mechanical-software-inc/MS1_board/Kristerj.kicad_sch

## KiCad design Kristerj.kicad_sch (2024-08-09)

Schematic: Kristerj.kicad_sch

Parts:
C1, C2, C3, C4: 47uF; C_1206_3216Metric; Mfg PN C3216X5R1E476M160AC
C5: 22uF; C_0603_1608Metric; Mfg PN GRM188R61A226ME15D
C6, C7, C18, C19, C31, C32, C37, C41, C42, C43, C44, C45, C46, C47, C48, C49, C50, C51, C52, C53, C54, C55, C56, C57, C58, C59, C60, C64, C66, C68: 100nF; C_0603_1608Metric; Mfg PN C1608X7R1H104K080AA
C8, C9, C20, C21, C33, C61: 1uF; C_0603_1608Metric; Mfg PN CL10A105KL8NNNC
C10, C13, C16, C17, C24, C25, C28, C29, C36, C40: 0.01uF; C_0603_1608Metric; Mfg PN C0603C103K5RAC7867
C11, C12, C14, C15, C22, C23, C26, C27, C35, C39: 220pF; C_0603_1608Metric; Mfg PN 06035A221JAT2A
C30: .022uF; C_0603_1608Metric; Mfg PN CGA3E2X7R1H223K080AA
C34, C38, C63, C65, C67, C69: T491A106K010AT; C_1206_3216Metric; Mfg PN T491A106K010AT
C62: 470pF; C_0603_1608Metric; Mfg PN GCM1885C2A471JA16D
D1, D2, D3, D4, D5, D6, D7, D8, D9, D10, D11, D12, D13, D14, D23, D24, D25, D26, D27, D28, D29, D30, D31, D32, D33, D34, D35, D36, D45, D47, D49, D50, D51, D53, D54, D55, D56, D57: 3.9V; D_SOD-323; Mfg PN MM3Z3V9ST1G
D15, D16, D21, D22, D37, D38, D43, D44, D59, D65: 5A; D_SMC; Mfg PN VS-5ECH06-M3/9AT
D17, D18, D19, D20, D39, D40, D41, D42, D63, D64: D; D_DO-41_SOD81_P7.62mm_Horizontal; Mfg PN 1N4007-T
F1: 3A; Fuse_Bourns_MF-RHT200; Mfg PN MF-RHT200/32-2
FB1: 28C0236-0JW-10; LairdTech_28C0236-0JW-10; Mfg PN 28C0236-0JW-10
H1, H3, H4, H5, H8, H11: MountingHole; MountingHole_5.5mm; Mfg PN DNP
H2, H6, H7, H9, H10, H12, H13: MountingHole; MountingHole_3.5mm; Mfg PN DNP
IC1, IC2, IC3, IC4, IC5, IC6: LM4040C30FTA; SOT-23; Mfg PN LM4040C30FTA
J1: 24V IN; 1945096; Mfg PN 1945096
J2: +24V IN; BarrelJack_CUI_PJ-102AH_Horizontal; Mfg PN PJ-102AH
J3_1, J3_2, J4_1, J4_2, J9_1, J9_2, J10_1, J10_2, J11_1, J11_2, J12_1, J12_2, J15_1, J15_2, J16_1, J16_2, J17_1, J17_2, J18_1, J18_2, J21_1, J21_2: Screw_Terminal_01x04; PhoenixContact_MSTBA_2,5_4-G-5,08_1x04_P5.08mm_Horizontal; Mfg PN 1757268
J4: 5-2301994-9; TE_5-2301994-9; PARTREV A1
J5, J6, J13, J14, J19, J20: Conn_01x03; PinSocket_1x03_P2.54mm_Vertical; Mfg PN 215299-3
J7: Conn_01x02; 1945096; Mfg PN 1945096
J8: Conn_02x20_Odd_Even; PinHeader_2x20_P2.54mm_Vertical; Mfg PN 6-103169-8
JP1, JP2, JP3, JP4, JP5, JP6, JP7, JP8, JP9, JP10, JP11, JP12: SolderJumper_3_Open; SolderJumper-3_P1.3mm_Open_RoundedPad1.0x1.5mm
L1: 22uH; L_Radial_D7.0mm_P3.00mm; Mfg PN RLB0712-220KL
PS1: K7805-3AR3; CONV_K7805-3AR3; Mfg PN K7805-3AR3
Q1, Q2, Q7, Q8, Q13, Q14, Q19, Q20, Q25, Q31: DMN10H220L; SOT-23; Mfg PN DMN10H220L-7
Q3, Q4, Q9, Q10, Q15, Q16, Q21, Q22, Q27, Q33: RD3P130S; TO-252-2; Mfg PN RD3P130SPFRATL
Q5, Q6, Q17, Q18, Q30: NDC7002N; SOT-23-6; Mfg PN NDC7002N
Q11, Q12, Q23, Q24, Q36: IRF9Z24S; TO-263-2; Mfg PN IRF9Z24SPBF
Q37, Q38, Q39, Q40, Q41, Q42, Q43, Q44, Q45, Q46: MMBT3904; SOT-23; Mfg PN MMBT3904
R1, R3, R7, R9, R14, R16, R29, R31, R77, R79, R81, R83, R89, R92, R103, R105, R149, R153, R160, R175: 68K; R_0603_1608Metric; Mfg PN RC0603FR-0768KL
R2, R4, R8, R10, R11, R15, R17, R18, R19, R20, R22, R25, R30, R32, R33, R34, R35, R36, R47, R48, R55, R57, R69, R72, R78, R80, R82, R84, R85, R88, R90, R91, R93, R94, R95, R98, R104, R106, R107, R108, R109, R110, R121, R122, R127, R129, R143, R144, R150, R154, R157, R158, R161, R165, R166, R167, R169, R176, R179, R180, R181, R182, R193, R201, R215, R221, R222, R223, R224, R225, R226, R227, R228, R229, R230, R231, R232, R233, R234, R235, R236, R237, R238, R239, R240, R241, R242, R243, R244, R245, R246, R247, R248, R249, R250: 10K; R_0603_1608Metric; Mfg PN ERJ-3GEYJ103V
R5, R6, R49, R54: 5.1K; R_0603_1608Metric; Mfg PN ERJ-3EKF5101V
R12, R13, R21, R23, R27, R28, R42, R44, R64, R67, R86, R87, R96, R97, R101, R102, R116, R119, R136, R139, R159, R162, R168, R170, R173, R174, R188, R208: 150; R_0603_1608Metric; Mfg PN CR0603-JW-151ELF
R24, R26, R37, R38, R60, R62, R99, R100, R111, R113, R133, R134, R171, R172, R183, R205: 1K; R_0603_1608Metric; Mfg PN CR0603-FX-1001ELF
R39, R40, R112, R114, R185: 16K; R_0603_1608Metric; Mfg PN RK73H1JTTD1800F
R41, R43, R63, R66, R115, R118, R135, R138, R187, R207: 3.3K; R_0603_1608Metric; Mfg PN RC0603JR-103K3L
R45, R46, R65, R68, R117, R120, R137, R142, R189, R211: 100K; R_0603_1608Metric; Mfg PN RC0603JR-07100KL
R50, R51, R52, R53, R70, R71, R73, R76, R123, R124, R125, R126, R140, R141, R147, R148, R195, R198, R213, R219: 100; R_0603_1608Metric; Mfg PN RC0603FR-07100RL
R56, R58, R128, R130, R202: 6.2K; R_0603_1608Metric; Mfg PN CRCW06036K20FKEAC
R59, R61, R131, R132, R204: 249; R_0603_1608Metric; Mfg PN RK73H1JTTD2490F
R74, R75, R145, R146, R218: 22.1; R_0603_1608Metric; Mfg PN RK73H1JTTD22R1F
R251, R252, R253, R254: 10; R_0603_1608Metric; Mfg PN RMCF0603FT10R0
R255: 1.5k; R_0603_1608Metric; Mfg PN RC0603JR-071K5L
R256, R257, R258: 33; R_0603_1608Metric; Mfg PN RC0603FR-0733R2L
R259, R260: 332; R_0603_1608Metric; Mfg PN RMCF0603FT332R
R261: 12.1k; R_0603_1608Metric; Mfg PN RMCF0603FT12K1
U1, U2, U9, U10, U17, U18: PICO_RP2040; Rasp_Pi_PICO; Mfg PN M20-7822046
U3, U4, U7, U25, U26, U27: MCP3428x-xST; TSSOP-14_4.4x5mm_P0.65mm; Mfg PN MCP3428-E/ST
U5, U6, U13, U14, U22: Opamp_Dual_Generic; DFN-8-1EP_3x3mm_P0.5mm_EP1.65x2.38mm; Mfg PN LT1490ACDD#TRPBF
U8: LAN8720A; VQFN-24-1EP_4x4mm_P0.5mm_EP2.5x2.5mm_ThermalVias; Mfg PN LAN8720AI-CP-TR
U11: 24AA256UIDT-I/SN; SOIC-8_3.9x4.9mm_P1.27mm; Mfg PN 24AA256UIDT-I/SN
X1: ECS-2033-500-BN; Oscillator_SMD_ECS_2520MV-xxx-xx-4Pin_2.5x2.0mm; Mfg PN ECS-2033-500-BN

Connections:
3.3V_1: JP1.3 (B), JP7.3 (B), R35.2, R227.2, U2.36 (3V3)
3.3V_2: JP2.3 (B), JP8.3 (B), R107.2, R228.2, U9.36 (3V3)
3.3V_3: JP3.3 (B), JP9.3 (B), R179.2, R229.2, U17.36 (3V3)
3.3V_4: JP4.3 (B), JP10.3 (B), R33.2, R230.2, U1.36 (3V3)
3.3V_5: JP5.3 (B), JP11.3 (B), R109.2, R231.2, U10.36 (3V3)
3.3V_6: C60.1, FB1.2, JP6.3 (B), JP12.3 (B), R181.2, R232.2, R253.2, R255.2, U8.9 (VDDIO), U18.36 (3V3), X1.4 (VDD)
+5V: C5.2, C32.1, C34.1, C37.1, C38.1, C41.1, C63.1, C64.1, C65.1, C66.1, C67.1, C68.1, C69.1, J8.2, J8.4, PS1.9 (+VO1), PS1.10 (+VO1), R5.2, R6.2, R20.2, R24.1, R25.2, R26.1, R41.2, R43.2, R49.2, R54.2, R63.2, R66.2, R94.2, R95.2, R98.2, R99.1, R100.1, R115.2, R118.2, R135.2, R138.2, R165.2, R166.2, R167.2, R169.2, R171.1, R172.1, R187.2, R207.2, U1.40 (VBUS), U2.40 (VBUS), U3.6 (V_{DD}), U3.9 (Adr0), U4.6 (V_{DD}), U4.9 (Adr0), U7.6 (V_{DD}), U7.9 (Adr0), U7.10 (Adr1), U9.40 (VBUS), U10.40 (VBUS), U11.8 (VCC), U17.40 (VBUS), U18.40 (VBUS), U25.6 (V_{DD}), U26.6 (V_{DD}), U26.10 (Adr1), U27.6 (V_{DD})
+24V: C8.1, C9.1, C10.2, C13.2, C16.2, C17.2, C20.1, C21.1, C24.2, C25.2, C28.2, C29.2, C33.1, C36.2, C40.2, D17.1 (K), D19.1 (K), D39.1 (K), D41.1 (K), D63.1 (K), F1.1, J1.1, J2.1, J3_1.2, J3_1.4, J3_2.1, J3_2.4, J4_1.2, J4_1.4, J4_2.1, J4_2.4, J11_1.2, J11_1.4, J11_2.1, J11_2.4, J12_1.2, J12_1.4, J12_2.1, J12_2.4, J17_1.2, J17_1.4, J17_2.1, J17_2.4, J18_1.2, J18_1.4, J18_2.1, J18_2.4, Q3.3 (S), Q4.3 (S), Q9.3 (S), Q10.3 (S), Q15.3 (S), Q16.3 (S), Q21.3 (S), Q22.3 (S), Q27.3 (S), Q33.3 (S), R47.2, R48.2, R55.2, R57.2, R59.2, R61.2, R69.2, R72.2, R121.2, R122.2, R127.2, R129.2, R131.2, R132.2, R143.2, R144.2, R193.2, R201.2, R204.2, R215.2, U5.8 (V+), U6.8 (V+), U13.8 (V+), U14.8 (V+), U22.8 (V+)
ADC_REF1: IC2.1 (CATHODE), R26.2, U2.35 (ADC_VREF)
ADC_REF2: IC3.1 (CATHODE), R99.2, U9.35 (ADC_VREF)
ADC_REF3: IC5.1 (CATHODE), R171.2, U17.35 (ADC_VREF)
ADC_REF4: IC1.1 (CATHODE), R24.2, U1.35 (ADC_VREF)
ADC_REF5: IC4.1 (CATHODE), R100.2, U10.35 (ADC_VREF)
ADC_REF6: IC6.1 (CATHODE), R172.2, U18.35 (ADC_VREF)
AVDD: C30.2, FB1.1, J4.P9, J4.P12, U8.1 (VDD2A), U8.19 (VDD1A)
CRS: R254.2, U18.11 (GP8)
GND: C1.1, C2.1, C3.1, C4.1, C5.1, C6.2, C7.2, C8.2, C9.2, C18.2, C19.2, C20.2, C21.2, C30.1, C31.2, C32.2, C33.2, C34.2, C37.2, C38.2, C41.2, C42.2, C43.2, C44.2, C45.2, C46.2, C47.2, C48.2, C49.2, C50.2, C51.2, C52.2, C53.2, C54.2, C55.2, C56.2, C57.2, C58.2, C59.2, C60.2, C61.2, C62.1, C63.2, C64.2, C65.2, C66.2, C67.2, C68.2, C69.2, D1.2 (A), D2.2 (A), D3.2 (A), D4.2 (A), D5.2 (A), D6.2 (A), D7.2 (A), D8.2 (A), D9.2 (A), D10.2 (A), D11.2 (A), D12.2 (A), D13.2 (A), D14.2 (A), D18.2 (A), D20.2 (A), D23.2 (A), D24.2 (A), D25.2 (A), D26.2 (A), D27.2 (A), D28.2 (A), D29.2 (A), D30.2 (A), D31.2 (A), D32.2 (A), D33.2 (A), D34.2 (A), D35.2 (A), D36.2 (A), D40.2 (A), D42.2 (A), D45.2 (A), D47.2 (A), D49.2 (A), D50.2 (A), D51.2 (A), D53.2 (A), D54.2 (A), D55.2 (A), D56.2 (A), D57.2 (A), D64.2 (A), IC1.2 (ANODE_1), IC1.3 (ANODE_2), IC2.2 (ANODE_1), IC2.3 (ANODE_2), IC3.2 (ANODE_1), IC3.3 (ANODE_2), IC4.2 (ANODE_1), IC4.3 (ANODE_2), IC5.2 (ANODE_1), IC5.3 (ANODE_2), IC6.2 (ANODE_1), IC6.3 (ANODE_2), J1.2, J2.2, J4.S1 (SHIELD), J4.S2 (SHIELD__1), J5.2, J6.2, J8.6, J8.9, J8.14, J8.20, J8.25, J8.30, J8.34, J8.39, J9_2.1, J9_2.3, J10_2.1, J10_2.3, J13.2, J14.2, J15_2.1, J15_2.3, J16_2.1, J16_2.3, J19.2, J20.2, J21_2.1, J21_2.3, JP1.1 (A), JP2.1 (A), JP3.1 (A), JP4.1 (A), JP5.1 (A), JP6.1 (A), JP7.1 (A), JP8.1 (A), JP9.1 (A), JP10.1 (A), JP11.1 (A), JP12.1 (A), PS1.5 (GND), PS1.6 (GND), PS1.7 (GND), PS1.8 (GND), Q1.2 (S), Q2.2 (S), Q7.2 (S), Q8.2 (S), Q13.2 (S), Q14.2 (S), Q19.2 (S), Q20.2 (S), Q25.2 (S), Q31.2 (S), Q37.2 (E), Q38.2 (E), Q39.2 (E), Q40.2 (E), Q41.2 (E), Q42.2 (E), Q43.2 (E), Q44.2 (E), Q45.2 (E), Q46.2 (E), R2.2, R4.2, R8.2, R10.2, R11.1, R12.1, R13.1, R15.2, R17.2, R18.1, R19.1, R21.1, R22.1, R23.1, R27.1, R28.1, R30.2, R32.2, R45.1, R46.1, R56.1, R58.1, R65.1, R68.1, R78.2, R80.2, R82.2, R84.2, R85.1, R86.1, R87.1, R88.1, R90.2, R91.1, R93.2, R96.1, R97.1, R101.1, R102.1, R104.2, R106.2, R117.1, R120.1, R128.1, R130.1, R137.1, R142.1, R150.2, R154.2, R157.1, R158.1, R159.1, R161.2, R162.1, R168.1, R170.1, R173.1, R174.1, R176.2, R189.1, R202.1, R211.1, R261.1, U1.3 (GND), U1.8 (GND), U1.13 (GND), U1.18 (GND), U1.23 (GND), U1.28 (GND), U1.33 (GND), U1.38 (GND), U2.3 (GND), U2.8 (GND), U2.13 (GND), U2.18 (GND), U2.23 (GND), U2.28 (GND), U2.33 (GND), U2.38 (GND), U3.2 (CH1-), U3.4 (CH2-), U3.5 (V_{SS}), U3.10 (Adr1), U3.12 (CH3-), U3.13 (CH4+), U3.14 (CH4-), U4.2 (CH1-), U4.4 (CH2-), U4.5 (V_{SS}), U4.12 (CH3-), U4.13 (CH4+), U4.14 (CH4-), U5.4 (V-), U6.4 (V-), U7.2 (CH1-), U7.4 (CH2-), U7.5 (V_{SS}), U7.12 (CH3-), U7.13 (CH4+), U7.14 (CH4-), U8.25 (VSS), U9.3 (GND), U9.8 (GND), U9.13 (GND), U9.18 (GND), U9.23 (GND), U9.28 (GND), U9.33 (GND), U9.38 (GND), U10.3 (GND), U10.8 (GND), U10.13 (GND), U10.18 (GND), U10.23 (GND), U10.28 (GND), U10.33 (GND), U10.38 (GND), U11.1 (A0), U11.2 (A1), U11.3 (A2), U11.4 (GND), U13.4 (V-), U14.4 (V-), U17.3 (GND), U17.8 (GND), U17.13 (GND), U17.18 (GND), U17.23 (GND), U17.28 (GND), U17.33 (GND), U17.38 (GND), U18.3 (GND), U18.8 (GND), U18.13 (GND), U18.18 (GND), U18.23 (GND), U18.28 (GND), U18.33 (GND), U18.38 (GND), U22.4 (V-), U25.2 (CH1-), U25.4 (CH2-), U25.5 (V_{SS}), U25.9 (Adr0), U25.12 (CH3-), U25.13 (CH4+), U25.14 (CH4-), U26.2 (CH1-), U26.4 (CH2-), U26.5 (V_{SS}), U26.9 (Adr0), U26.12 (CH3-), U26.13 (CH4+), U26.14 (CH4-), U27.2 (CH1-), U27.4 (CH2-), U27.5 (V_{SS}), U27.10 (Adr1), U27.12 (CH3-), U27.13 (CH4+), U27.14 (CH4-), X1.2 (GND)
MDC: U8.13 (MDC), U18.20 (GP15)
MDIO: U18.19 (GP14)
unnamed: C1.2, C2.2, F1.2, L1.1
unnamed: C3.2, C4.2, L1.2, PS1.2 (VIN), PS1.3 (VIN), PS1.4 (VIN)
unnamed: C6.1, R39.1, U5.3 (+)
unnamed: C7.1, R40.1, U6.3 (+)
unnamed: C10.1, D15.1 (K), R50.2
unnamed: C11.1, R52.2, U5.1
unnamed: C11.2, Q5.5 (S), R56.2, U5.2 (-)
unnamed: C12.1, R53.2, U6.1
unnamed: C12.2, Q6.5 (S), R58.2, U6.2 (-)
unnamed: C13.1, D16.1 (K), R51.2
unnamed: C14.1, Q11.3 (S), R59.1, U5.6 (-)
unnamed: C14.2, R70.2, U5.7
unnamed: C15.1, Q12.3 (S), R61.1, U6.6 (-)
unnamed: C15.2, R71.2, U6.7
unnamed: C16.1, D21.1 (K), R73.2
unnamed: C17.1, D22.1 (K), R76.2
unnamed: C18.1, R112.1, U13.3 (+)
unnamed: C19.1, R114.1, U14.3 (+)
unnamed: C22.1, R125.2, U13.1
unnamed: C22.2, Q17.5 (S), R128.2, U13.2 (-)
unnamed: C23.1, R126.2, U14.1
unnamed: C23.2, Q18.5 (S), R130.2, U14.2 (-)
unnamed: C24.1, D37.1 (K), R123.2
unnamed: C25.1, D38.1 (K), R124.2
unnamed: C26.1, Q23.3 (S), R131.1, U13.6 (-)
unnamed: C26.2, R140.2, U13.7
unnamed: C27.1, Q24.3 (S), R132.1, U14.6 (-)
unnamed: C27.2, R141.2, U14.7
unnamed: C28.1, D43.1 (K), R147.2
unnamed: C29.1, D44.1 (K), R148.2
unnamed: C31.1, R185.1, U22.3 (+)
unnamed: C35.1, R198.2, U22.1
unnamed: C35.2, Q30.5 (S), R202.2, U22.2 (-)
unnamed: C36.1, D59.1 (K), R195.2
unnamed: C39.1, Q36.3 (S), R204.1, U22.6 (-)
unnamed: C39.2, R213.2, U22.7
unnamed: C40.1, D65.1 (K), R219.2
unnamed: C61.1, C62.2, U8.6 (VDDCR)
unnamed: D5.1 (K), J4_1.3, R12.2, R233.1
unnamed: D6.1 (K), J3_1.3, R13.2, R242.1
unnamed: D9.1 (K), J4_1.1, R21.2, R234.1
unnamed: D10.1 (K), J3_1.1, R23.2, R243.1
unnamed: D11.1 (K), J4_2.3, R27.2, R235.1
unnamed: D12.1 (K), J3_2.3, R28.2, R244.1
unnamed: D17.2 (A), D18.1 (K), Q11.2 (D), R74.1
unnamed: D19.2 (A), D20.1 (K), Q12.2 (D), R75.1
unnamed: D27.1 (K), J12_1.3, R86.2, R236.1
unnamed: D28.1 (K), J11_1.3, R87.2, R245.1
unnamed: D31.1 (K), J12_1.1, R96.2, R237.1
unnamed: D32.1 (K), J11_1.1, R97.2, R246.1
unnamed: D33.1 (K), J12_2.3, R101.2, R238.1
unnamed: D34.1 (K), J11_2.3, R102.2, R247.1
unnamed: D39.2 (A), D40.1 (K), Q23.2 (D), R145.1
unnamed: D41.2 (A), D42.1 (K), Q24.2 (D), R146.1
unnamed: D49.1 (K), J18_1.3, R159.2, R239.1
unnamed: D50.1 (K), J17_1.3, R162.2, R248.1
unnamed: D53.1 (K), J18_1.1, R168.2, R240.1
unnamed: D54.1 (K), J17_1.1, R170.2, R249.1
unnamed: D55.1 (K), J18_2.3, R173.2, R241.1
unnamed: D56.1 (K), J17_2.3, R174.2, R250.1
unnamed: D63.2 (A), D64.1 (K), Q36.2 (D), R218.1
unnamed: J4.P1, U8.21 (TXP)
unnamed: J4.P2, U8.20 (TXN)
unnamed: J4.P3, U8.23 (RXP)
unnamed: J4.P6, U8.22 (RXN)
unnamed: J4.P10, R259.1
unnamed: J4.P11, R260.1
unnamed: JP1.2 (C), R36.1
unnamed: JP2.2 (C), R108.1
unnamed: JP3.2 (C), R180.1
unnamed: JP4.2 (C), R34.1
unnamed: JP5.2 (C), R110.1
unnamed: JP6.2 (C), R182.1
unnamed: JP7.2 (C), R221.1
unnamed: JP8.2 (C), R222.1
unnamed: JP9.2 (C), R223.1
unnamed: JP10.2 (C), R224.1
unnamed: JP11.2 (C), R225.1
unnamed: JP12.2 (C), R226.1
unnamed: Q1.1 (G), R42.1, R45.2
unnamed: Q1.3 (D), Q3.1 (G), R47.1
unnamed: Q2.1 (G), R44.1, R46.2
unnamed: Q2.3 (D), Q4.1 (G), R48.1
unnamed: Q5.1 (G), R52.1
unnamed: Q5.6 (D), R55.1, U5.5 (+)
unnamed: Q6.1 (G), R53.1
unnamed: Q6.6 (D), R57.1, U6.5 (+)
unnamed: Q7.1 (G), R64.1, R65.2
unnamed: Q7.3 (D), Q9.1 (G), R69.1
unnamed: Q8.1 (G), R67.1, R68.2
unnamed: Q8.3 (D), Q10.1 (G), R72.1
unnamed: Q11.1 (G), R70.1
unnamed: Q12.1 (G), R71.1
unnamed: Q13.1 (G), R116.1, R117.2
unnamed: Q13.3 (D), Q15.1 (G), R121.1
unnamed: Q14.1 (G), R119.1, R120.2
unnamed: Q14.3 (D), Q16.1 (G), R122.1
unnamed: Q17.1 (G), R125.1
unnamed: Q17.6 (D), R127.1, U13.5 (+)
unnamed: Q18.1 (G), R126.1
unnamed: Q18.6 (D), R129.1, U14.5 (+)
unnamed: Q19.1 (G), R136.1, R137.2
unnamed: Q19.3 (D), Q21.1 (G), R143.1
unnamed: Q20.1 (G), R139.1, R142.2
unnamed: Q20.3 (D), Q22.1 (G), R144.1
unnamed: Q23.1 (G), R140.1
unnamed: Q24.1 (G), R141.1
unnamed: Q25.1 (G), R188.1, R189.2
unnamed: Q25.3 (D), Q27.1 (G), R193.1
unnamed: Q30.1 (G), R198.1
unnamed: Q30.6 (D), R201.1, U22.5 (+)
unnamed: Q31.1 (G), R208.1, R211.2
unnamed: Q31.3 (D), Q33.1 (G), R215.1
unnamed: Q36.1 (G), R213.1
unnamed: Q37.1 (B), R37.2
unnamed: Q37.3 (C), R41.1, R42.2
unnamed: Q38.1 (B), R60.2
unnamed: Q38.3 (C), R63.1, R64.2
unnamed: Q39.1 (B), R38.2
unnamed: Q39.3 (C), R43.1, R44.2
unnamed: Q40.1 (B), R62.2
unnamed: Q40.3 (C), R66.1, R67.2
unnamed: Q41.1 (B), R113.2
unnamed: Q41.3 (C), R118.1, R119.2
unnamed: Q42.1 (B), R134.2
unnamed: Q42.3 (C), R138.1, R139.2
unnamed: Q43.1 (B), R183.2
unnamed: Q43.3 (C), R187.1, R188.2
unnamed: Q44.1 (B), R205.2
unnamed: Q44.3 (C), R207.1, R208.2
unnamed: Q45.1 (B), R111.2
unnamed: Q45.3 (C), R115.1, R116.2
unnamed: Q46.1 (B), R133.2
unnamed: Q46.3 (C), R135.1, R136.2
unnamed: R11.2, U1.24 (GP18)
unnamed: R18.2, U1.25 (GP19)
unnamed: R19.2, U2.26 (GP20)
unnamed: R20.1, U1.26 (GP20)
unnamed: R22.2, U2.25 (GP19)
unnamed: R25.1, U2.24 (GP18)
unnamed: R85.2, U9.24 (GP18)
unnamed: R88.2, U9.26 (GP20)
unnamed: R91.2, U10.25 (GP19)
unnamed: R94.1, U9.25 (GP19)
unnamed: R95.1, U10.26 (GP20)
unnamed: R98.1, U10.24 (GP18)
unnamed: R157.2, U17.26 (GP20)
unnamed: R158.2, U18.24 (GP18)
unnamed: R165.1, U17.25 (GP19)
unnamed: R166.1, U18.26 (GP20)
unnamed: R167.1, U17.24 (GP18)
unnamed: R169.1, U18.25 (GP19)
unnamed: R251.1, U8.8 (RXD0/MODE0)
unnamed: R252.1, U8.7 (RXD1/MODE1)
unnamed: R253.1, U8.10 (RXER/PHYAD0)
unnamed: R254.1, U8.11 (CRS_DV/MODE2)
unnamed: R255.1, U8.12 (MDIO)
unnamed: R257.1, R258.2, X1.3 (OUT)
unnamed: R259.2, U8.3 (LED1/REGOFF)
unnamed: R260.2, U8.2 (LED2/~INTSEL)
unnamed: R261.2, U8.24 (RBIAS)
OSCIN: R258.1, U8.5 (XTAL1/CLKIN)
Pi1_4-20_IN1: C42.1, R233.2, U2.31 (GP26), U25.1 (CH1+)
Pi1_4-20_IN2: C43.1, R234.2, U2.32 (GP27), U25.3 (CH2+)
Pi1_4-20_IN3: C44.1, R235.2, U2.34 (GP28), U25.11 (CH3+)
Pi1_4-20_OUT-1-: J4_2.2, R75.2
Pi1_4-20_OUT-2-: J12_2.2, R146.2
Pi1_4-20_OUT-3-: J18_2.2, R218.2
Pi1_4-20_OUT-4-: J3_2.2, R74.2
Pi1_4-20_OUT-5-: J11_2.2, R145.2
Pi1_4-20_OUT-6-: J17_2.2
Pi1_D-IN1: D2.1 (K), R3.2, R4.1, U2.4 (GP2)
Pi1_D-IN2: D4.1 (K), R9.2, R10.1, U2.5 (GP3)
Pi1_D-IN3: D8.1 (K), R16.2, R17.1, U2.6 (GP4)
Pi1_D-IN4: D14.1 (K), R31.2, R32.1, U2.7 (GP5)
Pi1_D-OUT1: R38.1, U2.9 (GP6)
Pi1_D-OUT3: R62.1, U2.11 (GP8)
Pi1_DI_1: J10_1.4, R3.1
Pi1_DI_2: J10_1.3, R9.1
Pi1_DI_3: J10_1.2, R16.1
Pi1_DI_4: J10_1.1, R31.1
Pi1_DO1: D16.2 (A), J10_2.4, Q4.2 (D), R51.1
Pi1_DO3: D22.2 (A), J10_2.2, Q10.2 (D), R76.1
Pi1_O_1: R40.2, U2.20 (GP15)
Pi1_O_2: R114.2, U9.20 (GP15)
Pi1_O_3: R185.2, U17.20 (GP15)
Pi1_O_4: R39.2, U1.20 (GP15)
Pi1_O_5: R112.2, U10.20 (GP15)
Pi1_RST: J8.7, U2.30 (RUN)
Pi1_SCL-1: J7.2, R6.1, U1.15 (GP11), U2.15 (GP11), U9.15 (GP11), U10.15 (GP11), U17.15 (GP11)
Pi1_SDA-1: J7.1, R5.1, U1.14 (GP10), U2.14 (GP10), U9.14 (GP10), U10.14 (GP10), U17.14 (GP10)
Pi1_SWCLK: J6.1, J8.5, R36.2, R221.2
Pi1_SWDIO: J6.3, J8.3, R35.1, R227.1
Pi2_4-20_IN1: C45.1, R236.2, U9.31 (GP26), U26.1 (CH1+)
Pi2_4-20_IN2: C46.1, R237.2, U9.32 (GP27), U26.3 (CH2+)
Pi2_4-20_IN3: C47.1, R238.2, U9.34 (GP28), U26.11 (CH3+)
Pi2_D-IN1: D23.1 (K), R77.2, R78.1, U9.4 (GP2)
Pi2_D-IN2: D25.1 (K), R81.2, R82.1, U9.5 (GP3)
Pi2_D-IN3: D29.1 (K), R89.2, R90.1, U9.6 (GP4)
Pi2_D-IN4: D35.1 (K), R103.2, R104.1, U9.7 (GP5)
Pi2_D-OUT1: R113.1, U9.9 (GP6)
Pi2_D-OUT3: R134.1, U9.11 (GP8)
Pi2_DI_1: J16_1.4, R77.1
Pi2_DI_2: J16_1.3, R81.1
Pi2_DI_3: J16_1.2, R89.1
Pi2_DI_4: J16_1.1, R103.1
Pi2_DO1: D38.2 (A), J16_2.4, Q16.2 (D), R124.1
Pi2_DO3: D44.2 (A), J16_2.2, Q22.2 (D), R148.1
Pi2_RST: J8.15, U9.30 (RUN)
Pi2_SWCLK: J8.13, J13.1, R108.2, R222.2
Pi2_SWDIO: J8.11, J13.3, R107.1, R228.1
Pi3_4-20_IN1: C48.1, R239.2, U17.31 (GP26), U27.1 (CH1+)
Pi3_4-20_IN2: C49.1, R240.2, U17.32 (GP27), U27.3 (CH2+)
Pi3_4-20_IN3: C50.1, R241.2, U17.34 (GP28), U27.11 (CH3+)
Pi3_D-IN1: D45.1 (K), R149.2, R150.1, U17.4 (GP2)
Pi3_D-IN2: D47.1 (K), R153.2, R154.1, U17.5 (GP3)
Pi3_D-IN3: D51.1 (K), R160.2, R161.1, U17.6 (GP4)
Pi3_D-IN4: D57.1 (K), R175.2, R176.1, U17.7 (GP5)
Pi3_D-OUT1: R183.1, U17.9 (GP6)
Pi3_D-OUT3: R205.1, U17.11 (GP8)
Pi3_DI_1: J21_1.4, R149.1
Pi3_DI_2: J21_1.3, R153.1
Pi3_DI_3: J21_1.2, R160.1
Pi3_DI_4: J21_1.1, R175.1
Pi3_DO1: D59.2 (A), J21_2.4, Q27.2 (D), R195.1
Pi3_DO3: D65.2 (A), J21_2.2, Q33.2 (D), R219.1
Pi3_RST: J8.23, U17.30 (RUN)
Pi3_SWCLK: J8.21, J19.1, R180.2, R223.2
Pi3_SWDIO: J8.19, J19.3, R179.1, R229.1
Pi4_4-20_IN1: C51.1, R242.2, U1.31 (GP26), U3.1 (CH1+)
Pi4_4-20_IN2: C52.1, R243.2, U1.32 (GP27), U3.3 (CH2+)
Pi4_4-20_IN3: C53.1, R244.2, U1.34 (GP28), U3.11 (CH3+)
Pi4_D-IN1: D1.1 (K), R1.2, R2.1, U1.4 (GP2)
Pi4_D-IN2: D3.1 (K), R7.2, R8.1, U1.5 (GP3)
Pi4_D-IN3: D7.1 (K), R14.2, R15.1, U1.6 (GP4)
Pi4_D-IN4: D13.1 (K), R29.2, R30.1, U1.7 (GP5)
Pi4_D-OUT1: R37.1, U1.9 (GP6)
Pi4_D-OUT3: R60.1, U1.11 (GP8)
Pi4_DI_1: J9_1.4, R1.1
Pi4_DI_2: J9_1.3, R7.1
Pi4_DI_3: J9_1.2, R14.1
Pi4_DI_4: J9_1.1, R29.1
Pi4_DO1: D15.2 (A), J9_2.4, Q3.2 (D), R50.1
Pi4_DO3: D21.2 (A), J9_2.2, Q9.2 (D), R73.1
Pi4_RST: J8.33, U1.30 (RUN)
Pi4_SWCLK: J5.1, J8.31, R34.2, R224.2
Pi4_SWDIO: J5.3, J8.29, R33.1, R230.1
Pi5_4-20_IN1: C54.1, R245.2, U4.1 (CH1+), U10.31 (GP26)
Pi5_4-20_IN2: C55.1, R246.2, U4.3 (CH2+), U10.32 (GP27)
Pi5_4-20_IN3: C56.1, R247.2, U4.11 (CH3+), U10.34 (GP28)
Pi5_D-IN1: D24.1 (K), R79.2, R80.1, U10.4 (GP2)
Pi5_D-IN2: D26.1 (K), R83.2, R84.1, U10.5 (GP3)
Pi5_D-IN3: D30.1 (K), R92.2, R93.1, U10.6 (GP4)
Pi5_D-IN4: D36.1 (K), R105.2, R106.1, U10.7 (GP5)
Pi5_D-OUT1: R111.1, U10.9 (GP6)
Pi5_D-OUT3: R133.1, U10.11 (GP8)
Pi5_DI_1: J15_1.4, R79.1
Pi5_DI_2: J15_1.3, R83.1
Pi5_DI_3: J15_1.2, R92.1
Pi5_DI_4: J15_1.1, R105.1
Pi5_DO1: D37.2 (A), J15_2.4, Q15.2 (D), R123.1
Pi5_DO3: D43.2 (A), J15_2.2, Q21.2 (D), R147.1
Pi5_RST: J8.26, U10.30 (RUN)
Pi5_SWCLK: J8.24, J14.1, R110.2, R225.2
Pi5_SWDIO: J8.22, J14.3, R109.1, R231.1
Pi6_4-20_IN1: C57.1, R248.2, U7.1 (CH1+), U18.31 (GP26)
Pi6_4-20_IN2: C58.1, R249.2, U7.3 (CH2+), U18.32 (GP27)
Pi6_4-20_IN3: C59.1, R250.2, U7.11 (CH3+), U18.34 (GP28)
Pi6_RST: J8.40, U18.30 (RUN)
Pi6_SWCLK: J8.38, J20.1, R182.2, R226.2
Pi6_SWDIO: J8.36, J20.3, R181.1, R232.1
REFCLKO: R256.1, U8.14 (~INT/REFCLKO)
RX0: R251.2, U18.9 (GP6)
RX1: R252.2, U18.10 (GP7)
R_RXCLK: R256.2, R257.2
SCL-0: J8.28, R54.1, U1.2 (GP1), U2.2 (GP1), U3.8 (SCL), U4.8 (SCL), U7.8 (SCL), U9.2 (GP1), U10.2 (GP1), U11.6 (SCL), U17.2 (GP1), U18.2 (GP1), U25.8 (SCL), U26.8 (SCL), U27.8 (SCL)
SDA-0: J8.27, R49.1, U1.1 (GP0), U2.1 (GP0), U3.7 (SDA), U4.7 (SDA), U7.7 (SDA), U9.1 (GP0), U10.1 (GP0), U11.5 (SDA), U17.1 (GP0), U18.1 (GP0), U25.7 (SDA), U26.7 (SDA), U27.7 (SDA)
TX0: U8.17 (TXD0), U18.14 (GP10)
TX1: U8.18 (TXD1), U18.15 (GP11)
TX_EN: U8.16 (TXEN), U18.16 (GP12)
nRST: U8.15 (~RST), U18.29 (GP22)

Notes on the sheet:
debug
To be programmed with inverted logic
ADDR(100)
(nRST)
Discrete Output - 6
DISCRETE
INPUT-OUTPUT
PI PICO - 2
4-20mA OUTPUT - 5
4-20mA INPUT - 5
Discrete Output - 1
(TX0)
4-20mA
GREEN
(MDC)
4-20mA OUTPUT - 3
(TX1)
Discrete Input - 3
YELLOW
Ethernet Port - 6
ADDR(110)
24AA256 I2C EEPROM
Discrete Input - 5
PI PICO - 1
4-20mA OUTPUT - 1
(GND)
ADDR(011)
4-20mA OUTPUT - 4
4-20mA INPUT - 3
(MDIO)
4-20mA INPUT - 4
(CRS)
RASPBERRY PI PICO 6
ADDR(001)
(RX0)
REMOVED 04-04-2024
RASPBERRY PI PICO 3
600mV to 3V
(3.3V_6)
(RX1)
ADDR(101)
Discrete Input - 6
4-20mA OUTPUT - 6
4-20mA OUTPUT - 2
PI PICO - 3
RASPBERRY PI PICO 2
Discrete Output - 3
(TX_EN)
PI PICO - 4
5V OUTPUT VOLTAGE REGULATOR
ADDED 04-04-2024
Discrete Output - 5
ADDED 04-09-2024
Discrete Input - 1
4-20mA INPUT - 6
4-20mA INPUT - 1
RASPBERRY PI PICO 1
Discrete Input - 4
4-20mA INPUT - 2
ADDR(010)
RASPBERRY PI PICO 5
PI PICO - 6
SWD CONNECTOR
Discrete Output - 4
Discrete Output - 2
PI PICO - 5
BUS I2C
VIN
Discrete Input - 2
RASPBERRY PI PICO 4
